Codru-Dragu/DLS_Synchronous_Diagnostics_Measurements/Software Package/src/BeamSchem.png

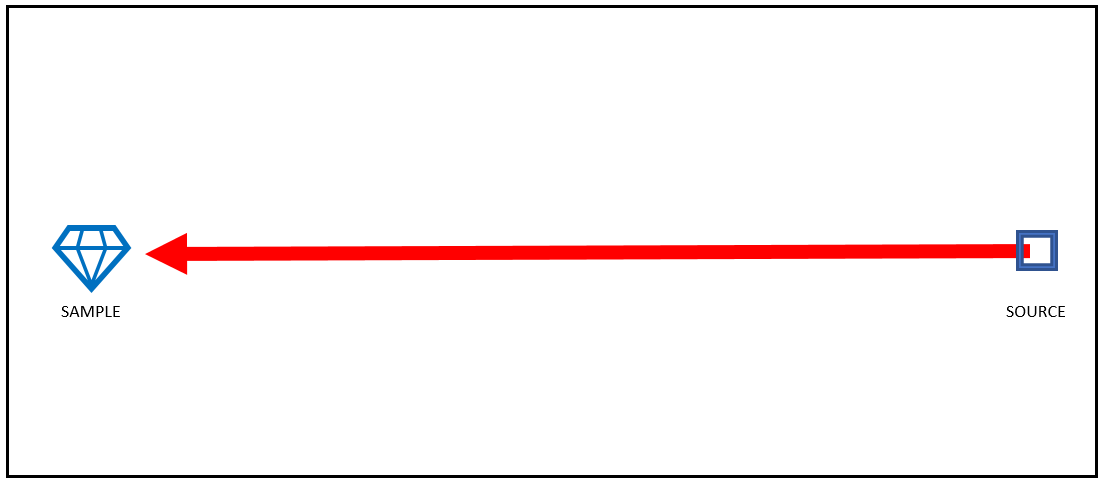
Software Package/src/BeamSchem.png
